yusenpai/zynq7000dev/demo/pcb/l1.png

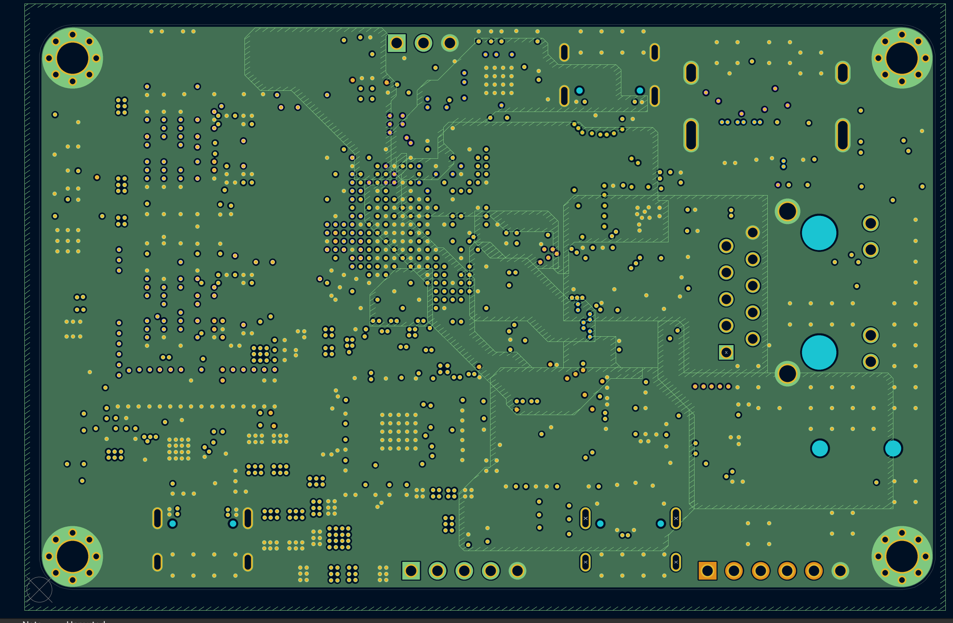
demo/pcb/l1.png
