yusenpai/zynq7000dev/demo/pcb/l4.png

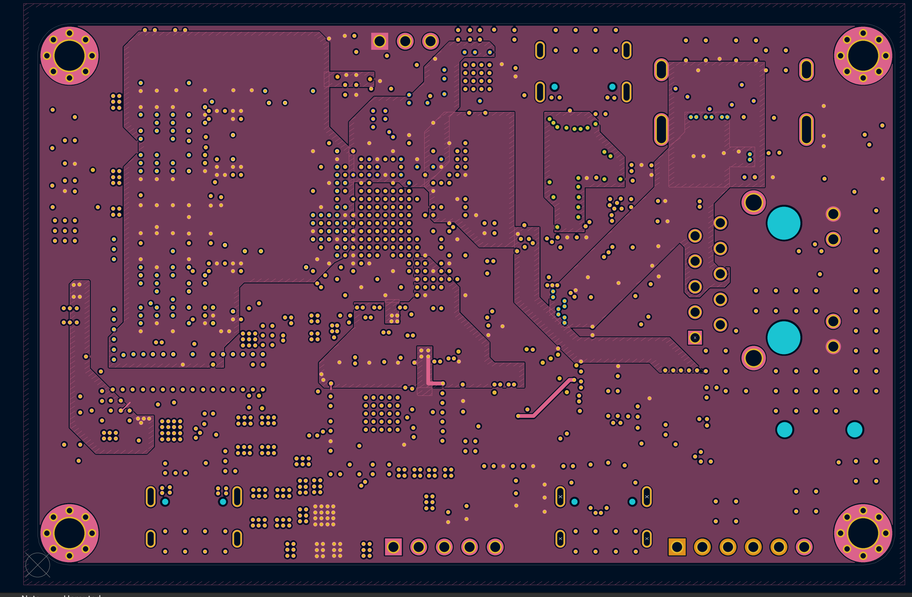
demo/pcb/l4.png
